meerstern/NanopiNeo-Neo2_ExtensionBoard/img/IMG_1.JPG

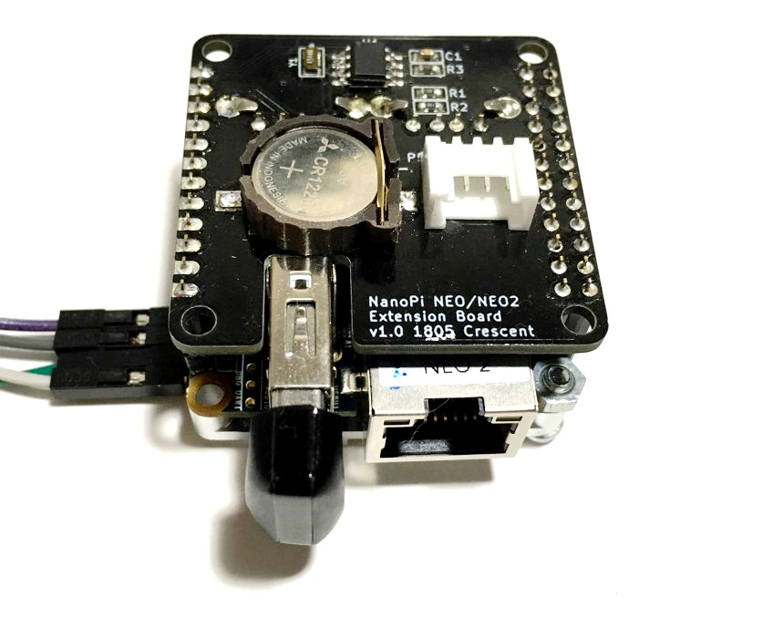
img/IMG_1.JPG
