meerstern/NanopiNeo-Neo2_ExtensionBoard/img/IMG_2.JPG

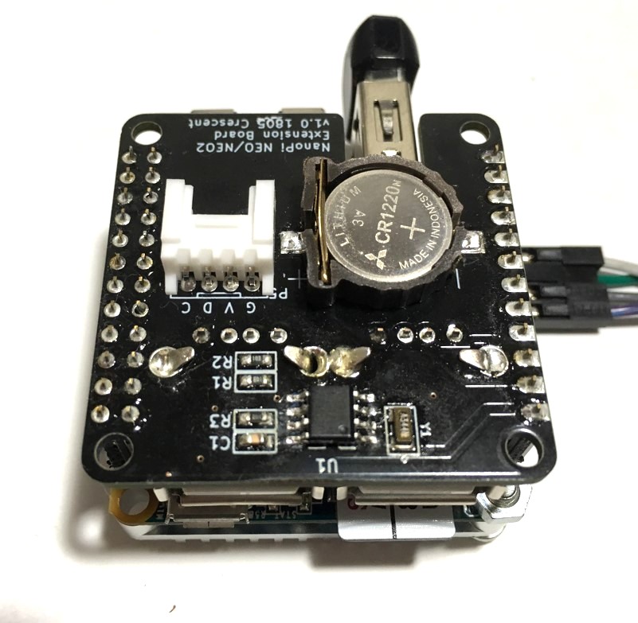
img/IMG_2.JPG
