meerstern/NanopiNeo-Neo2_ExtensionBoard/img/IMG_3.JPG

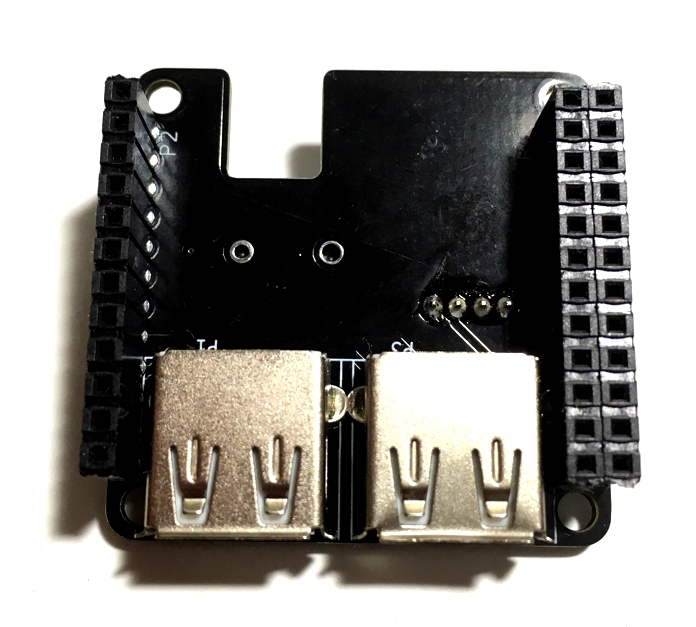
img/IMG_3.JPG
